DPHAD/Celestia-Retro-PC/CAD/Celestia DIY Retro CAD PC annotated.png

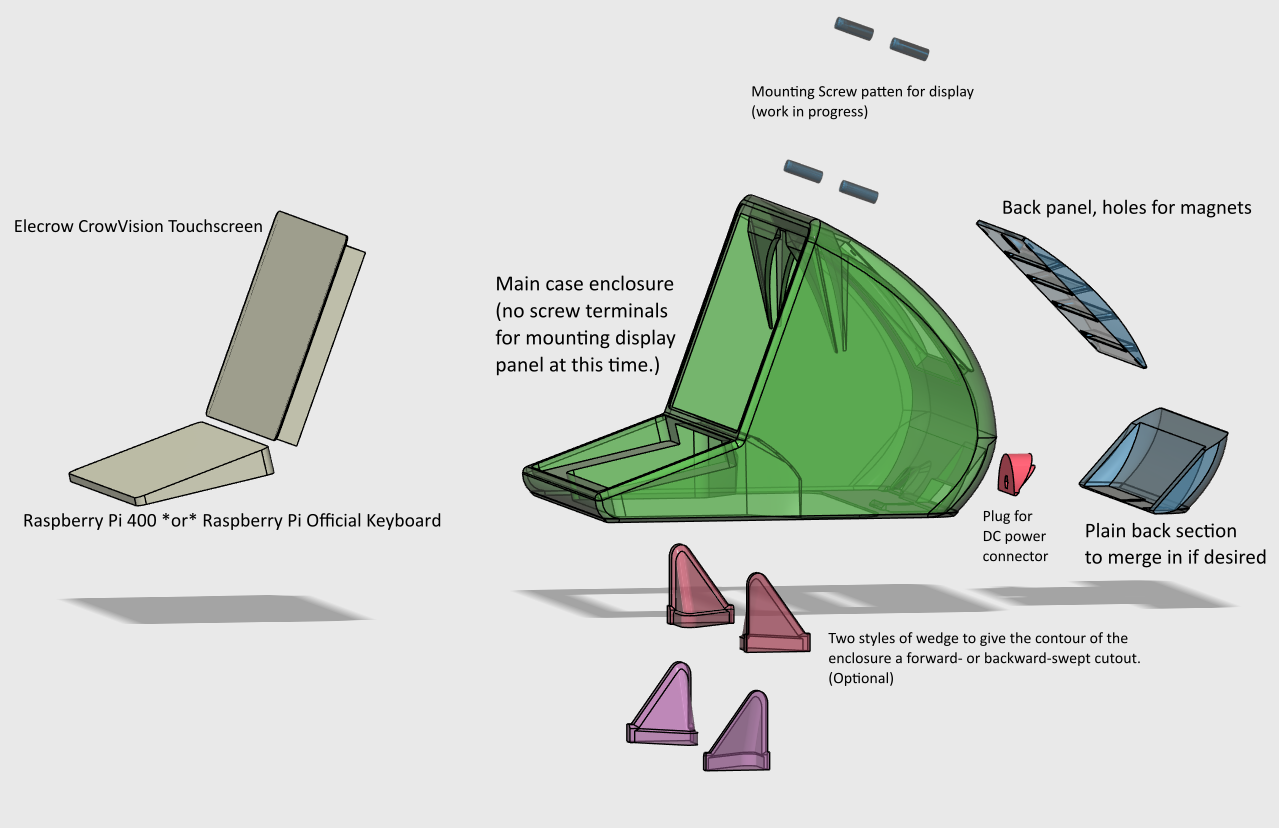
CAD/Celestia DIY Retro CAD PC annotated.png
