DPHAD/Celestia-Retro-PC/Images/Celestia Retro PC (1).jpg

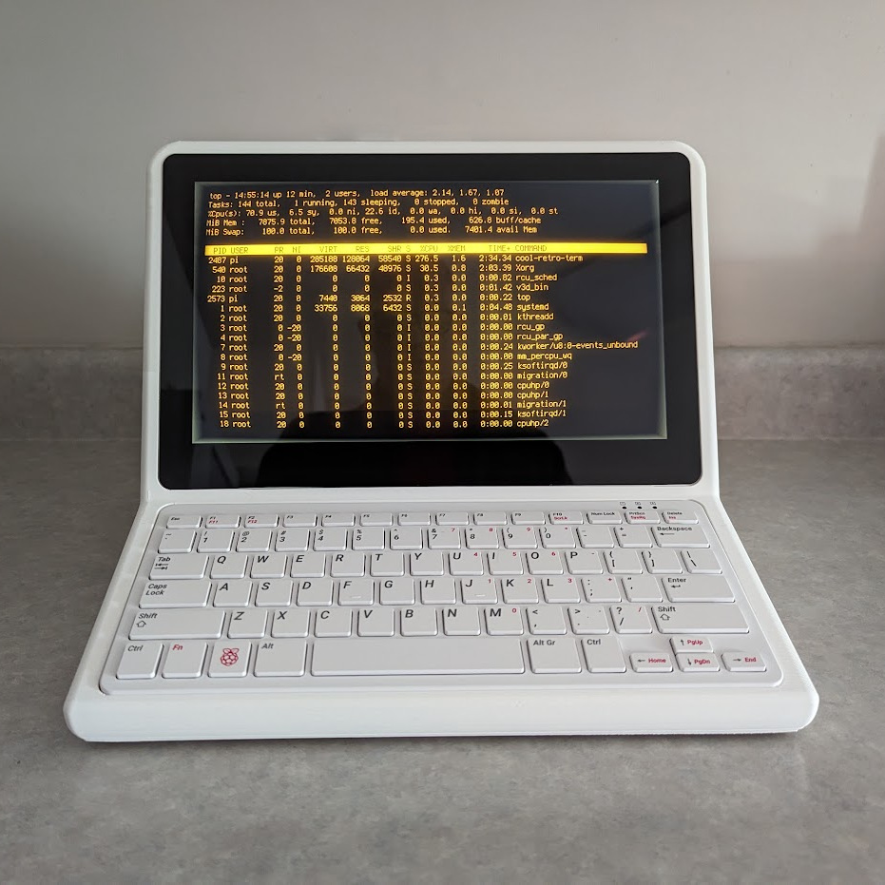
Images/Celestia Retro PC (1).jpg
